msinitcyn/robo-club-3d-models/artifacts/v1.2/lego_base_t.stl

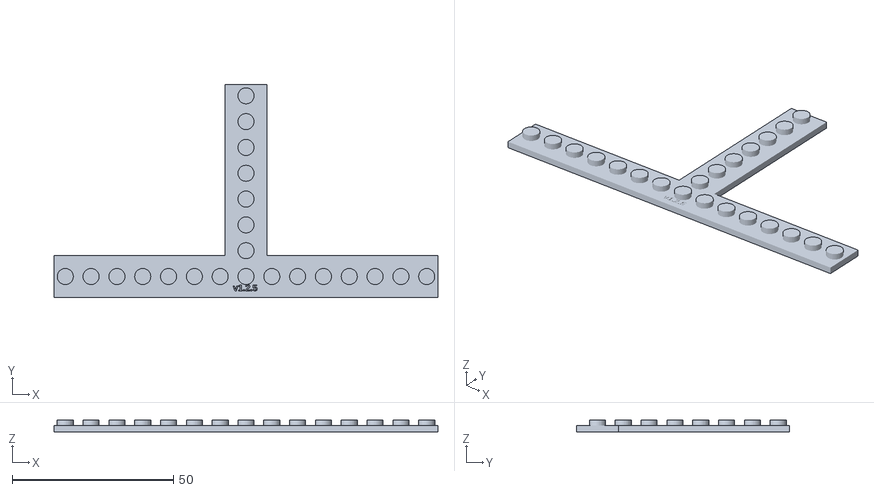
[picture p15: CAD file, 2025-12-20]
artifacts/v1.2/lego_base_t.stl
119.0 x 66.0 x 3.80
