msinitcyn/robo-club-3d-models/artifacts/current/lego_base_t.stl

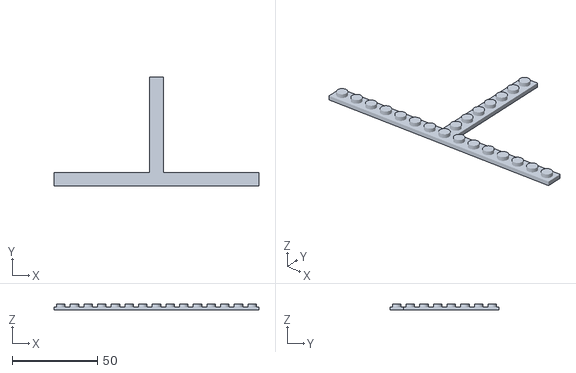
[picture p16: CAD file, 2025-12-21]
artifacts/current/lego_base_t.stl
120.0 x 64.0 x 3.80
