msinitcyn/robo-club-3d-models/artifacts/v1.2/corner_joint_dowel_flexible.stl

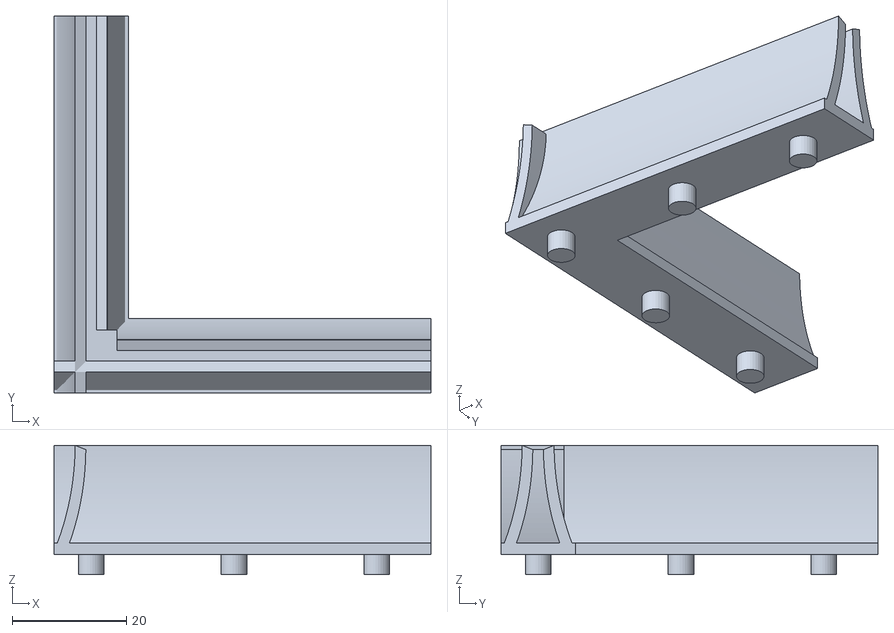
[picture p17: CAD file, 2025-12-20]
artifacts/v1.2/corner_joint_dowel_flexible.stl
66.0 x 66.0 x 22.6
