msinitcyn/robo-club-3d-models/artifacts/v1.2/lego_base_straight.stl

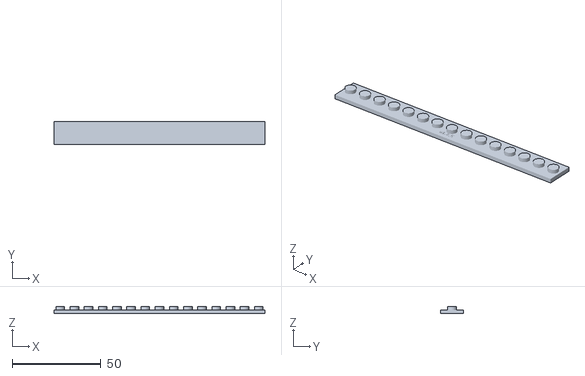
[picture p18: CAD file, 2025-12-20]
artifacts/v1.2/lego_base_straight.stl
119.0 x 13.0 x 3.80
