msinitcyn/robo-club-3d-models/artifacts/current/t_joint_dowel.stl

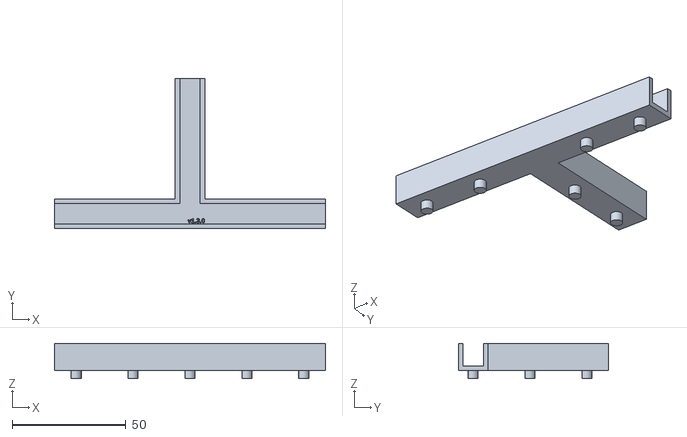
[picture p19: CAD file, 2025-12-21]
artifacts/current/t_joint_dowel.stl
119.0 x 66.0 x 15.5
