msinitcyn/robo-club-3d-models/artifacts/current/cross_joint_dowel.stl

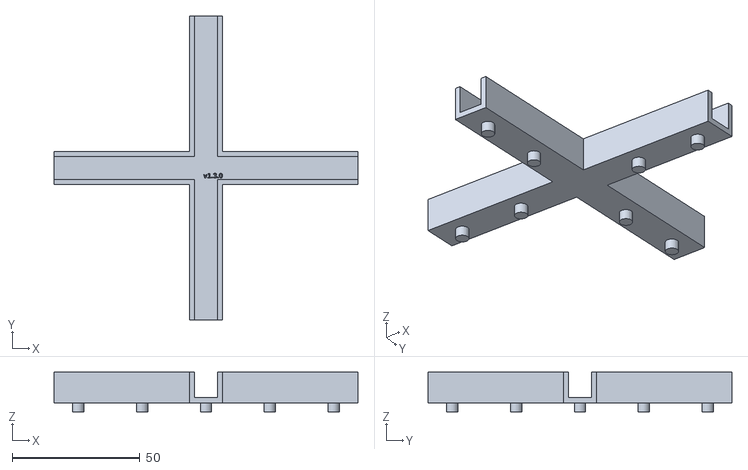
[picture p21: CAD file, 2025-12-21]
artifacts/current/cross_joint_dowel.stl
119.0 x 119.0 x 15.5
