msinitcyn/robo-club-3d-models/artifacts/current/lego_base_cross.stl

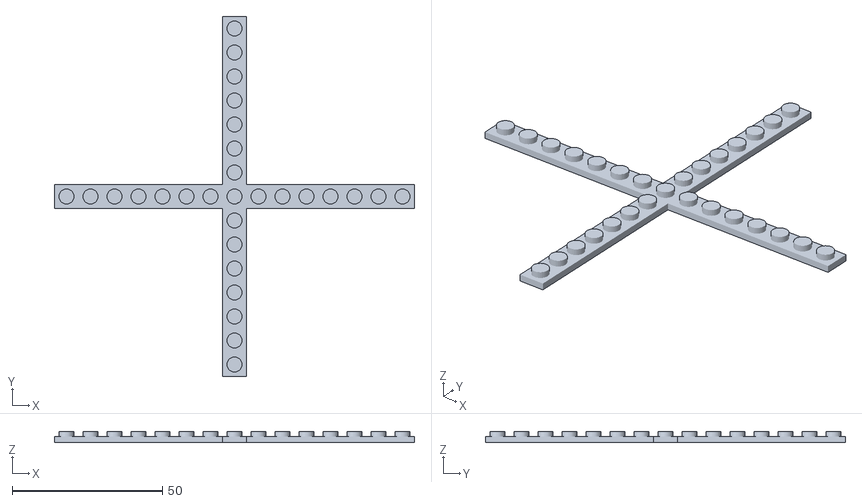
[picture p23: CAD file, 2025-12-21]
artifacts/current/lego_base_cross.stl
120.0 x 120.0 x 3.80
