msinitcyn/robo-club-3d-models/artifacts/current/lego_base_t_dowel.stl

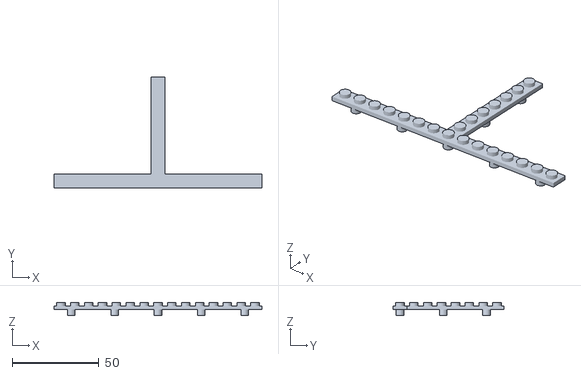
[picture p25: CAD file, 2025-12-21]
artifacts/current/lego_base_t_dowel.stl
120.0 x 64.0 x 7.30
