msinitcyn/robo-club-3d-models/artifacts/current/lego_wall_sleeve_flexible.stl

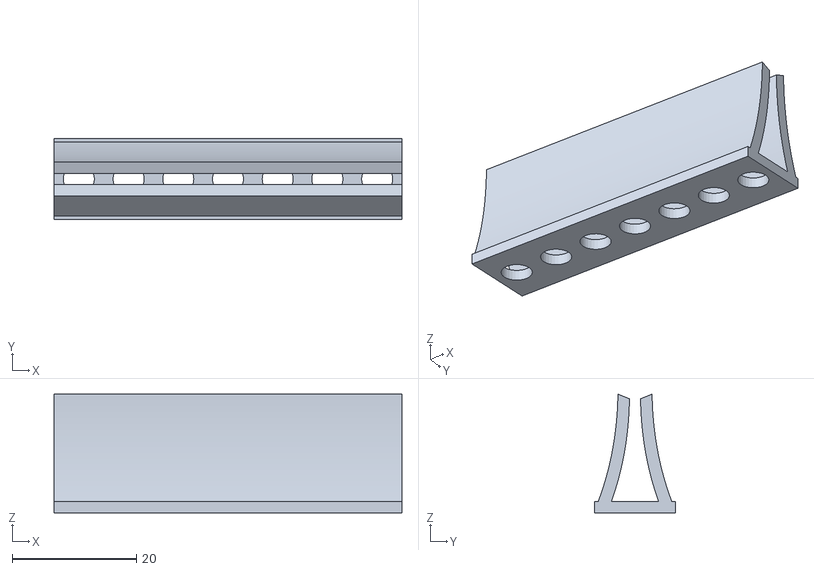
[picture p27: CAD file, 2025-12-21]
artifacts/current/lego_wall_sleeve_flexible.stl
56.0 x 13.0 x 19.1
