msinitcyn/robo-club-3d-models/artifacts/v1.2/straight_joint_dowel.stl

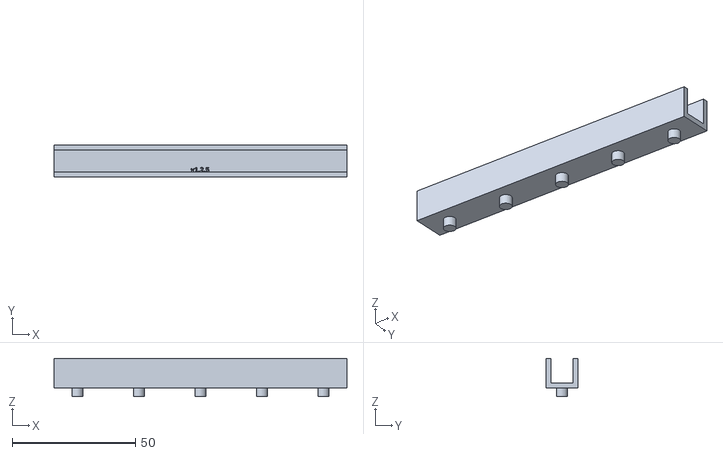
[picture p28: CAD file, 2025-12-20]
artifacts/v1.2/straight_joint_dowel.stl
119.0 x 13.0 x 15.5
