msinitcyn/robo-club-3d-models/artifacts/current/lego_base_cross_dowel.stl

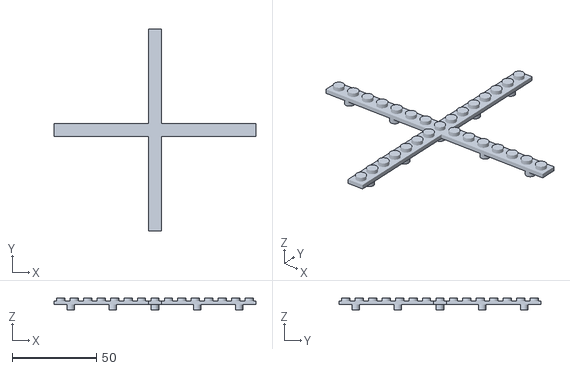
[picture p29: CAD file, 2025-12-21]
artifacts/current/lego_base_cross_dowel.stl
120.0 x 120.0 x 7.30
