msinitcyn/robo-club-3d-models/artifacts/current/lego_base_straight.stl

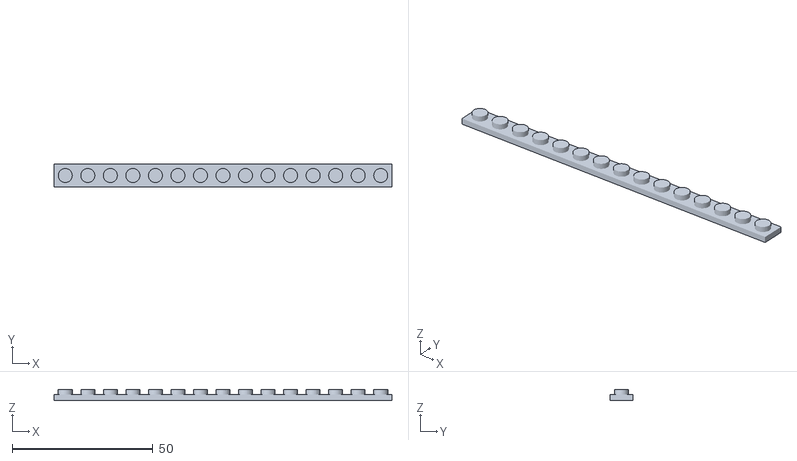
[picture p30: CAD file, 2025-12-21]
artifacts/current/lego_base_straight.stl
120.0 x 8.00 x 3.80
