msinitcyn/robo-club-3d-models/artifacts/current/t_joint_flexible.stl

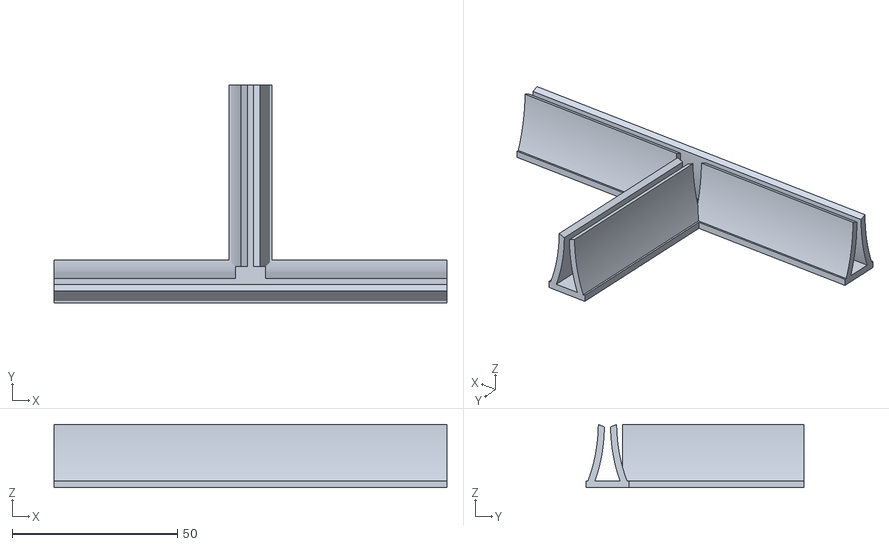
[picture p32: CAD file, 2025-12-21]
artifacts/current/t_joint_flexible.stl
119.0 x 66.0 x 19.1
