msinitcyn/robo-club-3d-models/artifacts/v1.2/lego_base_cross_dowel.stl

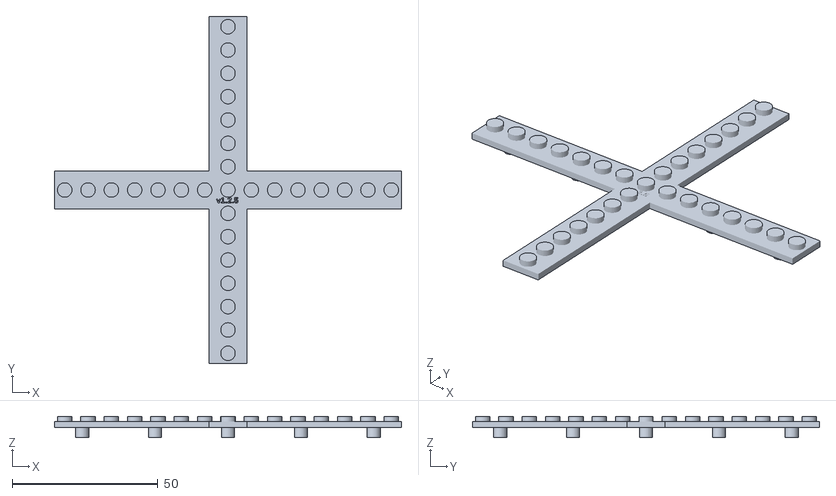
[picture p33: CAD file, 2025-12-20]
artifacts/v1.2/lego_base_cross_dowel.stl
119.0 x 119.0 x 7.30
