msinitcyn/robo-club-3d-models/artifacts/v1.2/lego_wall_sleeve_flexible.stl

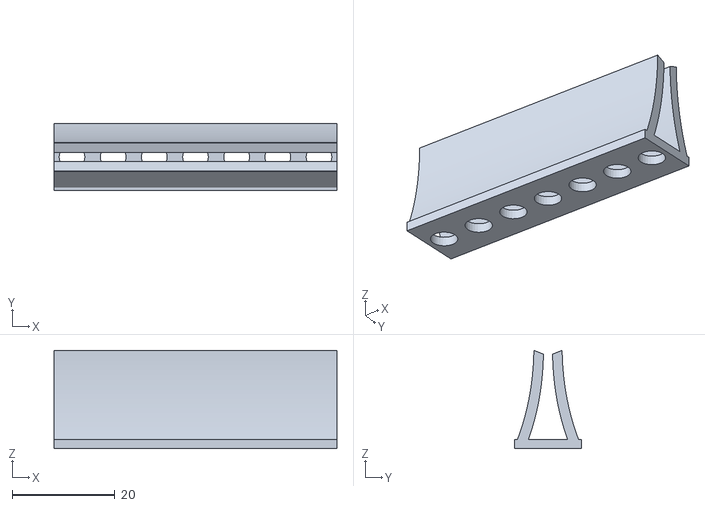
[picture p34: CAD file, 2025-12-20]
artifacts/v1.2/lego_wall_sleeve_flexible.stl
55.0 x 13.0 x 19.1
