msinitcyn/robo-club-3d-models/artifacts/v1.2/lego_base_corner_dowel.stl

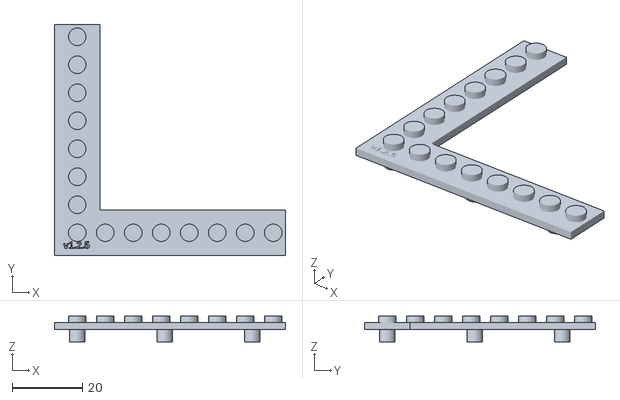
[picture p36: CAD file, 2025-12-20]
artifacts/v1.2/lego_base_corner_dowel.stl
66.0 x 66.0 x 7.30
