msinitcyn/robo-club-3d-models/artifacts/current/cross_joint_flexible.stl

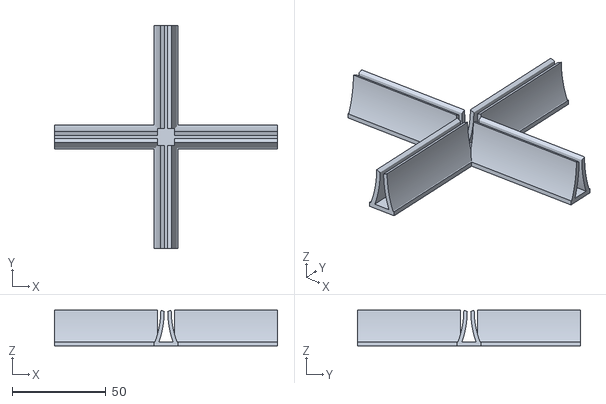
[picture p37: CAD file, 2025-12-21]
artifacts/current/cross_joint_flexible.stl
119.0 x 119.0 x 19.1
