msinitcyn/robo-club-3d-models/artifacts/v1.2/lego_base_t_dowel.stl

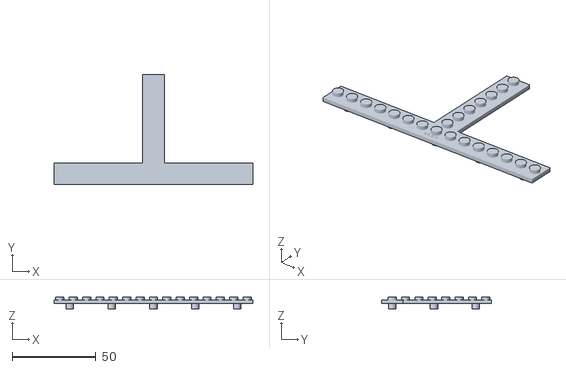
[picture p38: CAD file, 2025-12-20]
artifacts/v1.2/lego_base_t_dowel.stl
119.0 x 66.0 x 7.30
