msinitcyn/robo-club-3d-models/artifacts/v1.2/lego_wall_sleeve.stl

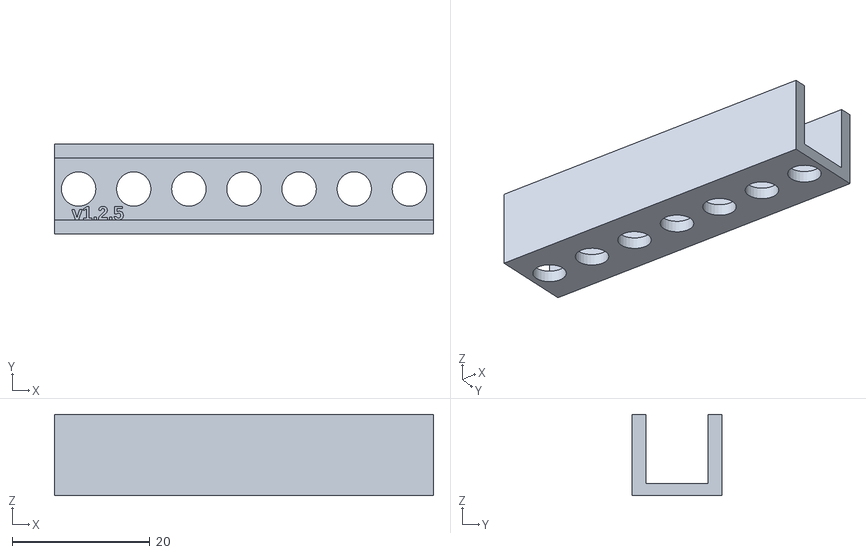
[picture p40: CAD file, 2025-12-19]
artifacts/v1.2/lego_wall_sleeve.stl
55.0 x 13.0 x 11.8
