msinitcyn/robo-club-3d-models/artifacts/current/lego_base_t_double.stl

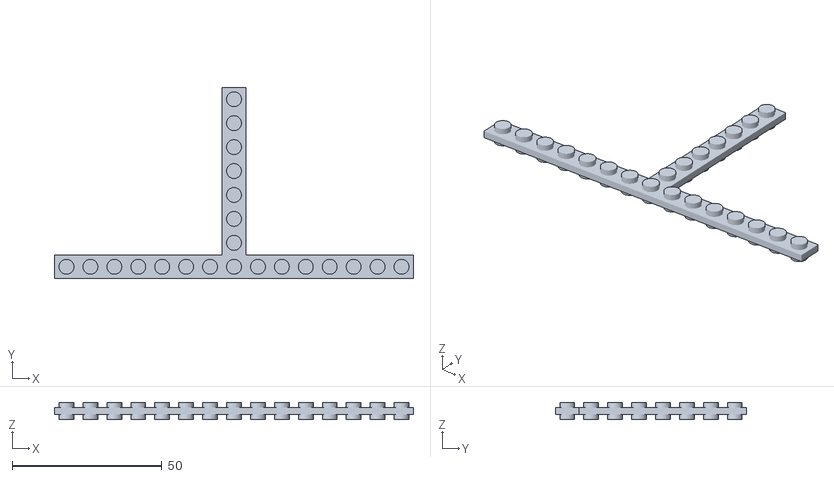
[picture p41: CAD file, 2025-12-21]
artifacts/current/lego_base_t_double.stl
120.0 x 64.0 x 5.80
