msinitcyn/robo-club-3d-models/artifacts/v1.2/cross_joint.stl

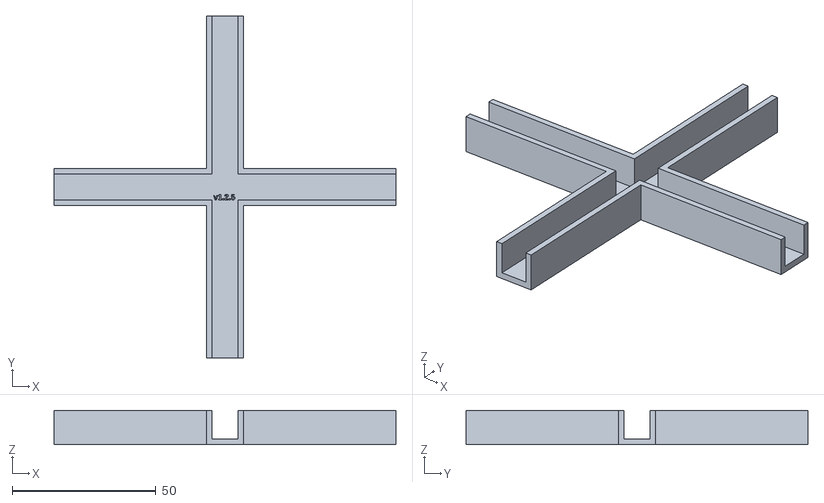
[picture p42: CAD file, 2025-12-19]
artifacts/v1.2/cross_joint.stl
119.0 x 119.0 x 12.0
