msinitcyn/robo-club-3d-models/artifacts/current/end_cap.stl

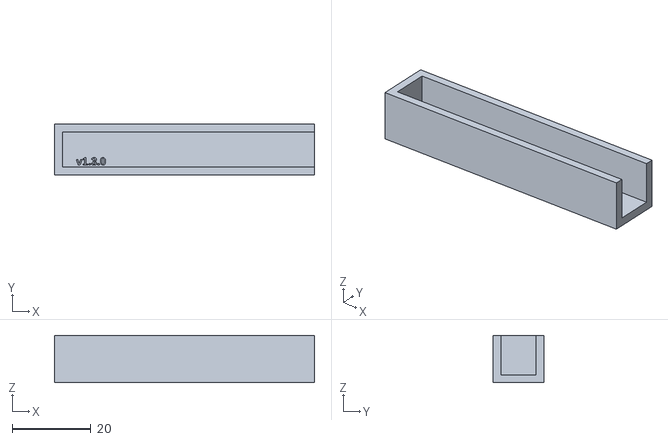
[picture p43: CAD file, 2025-12-21]
artifacts/current/end_cap.stl
66.0 x 13.0 x 12.0
