msinitcyn/robo-club-3d-models/artifacts/v1.2/corner_joint.stl

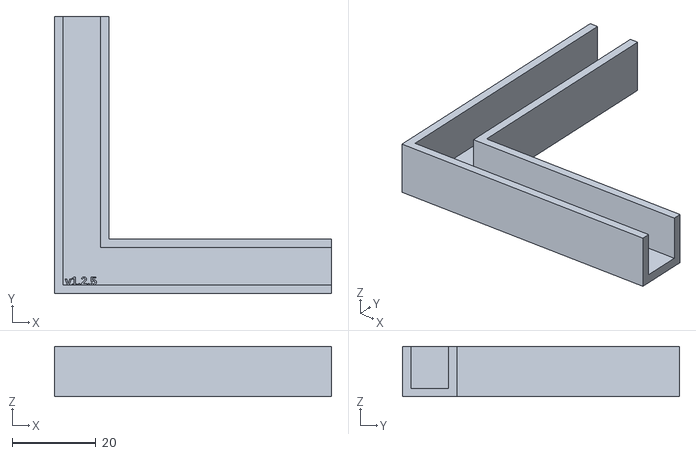
[picture p44: CAD file, 2025-12-19]
artifacts/v1.2/corner_joint.stl
66.0 x 66.0 x 12.0
