msinitcyn/robo-club-3d-models/artifacts/current/lego_wall_sleeve.stl

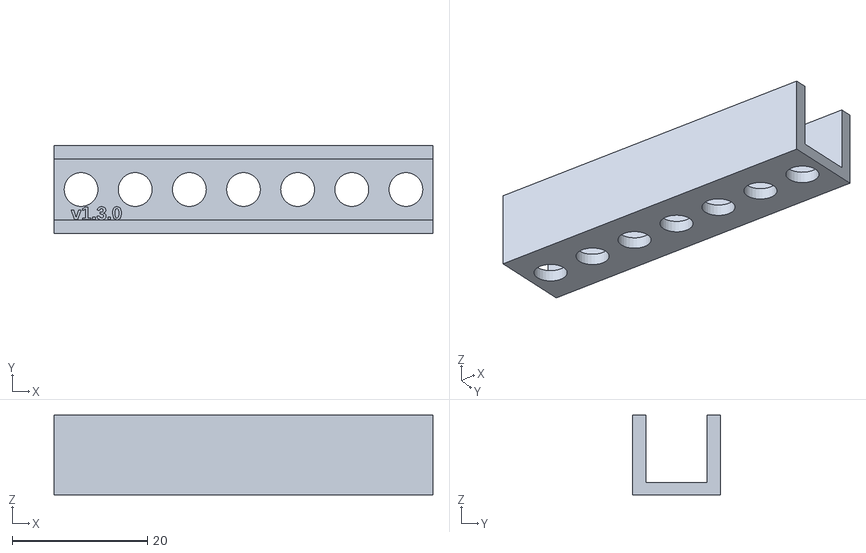
[picture p45: CAD file, 2025-12-21]
artifacts/current/lego_wall_sleeve.stl
56.0 x 13.0 x 11.8
