msinitcyn/robo-club-3d-models/artifacts/v1.2/end_cap_dowel_flexible.stl

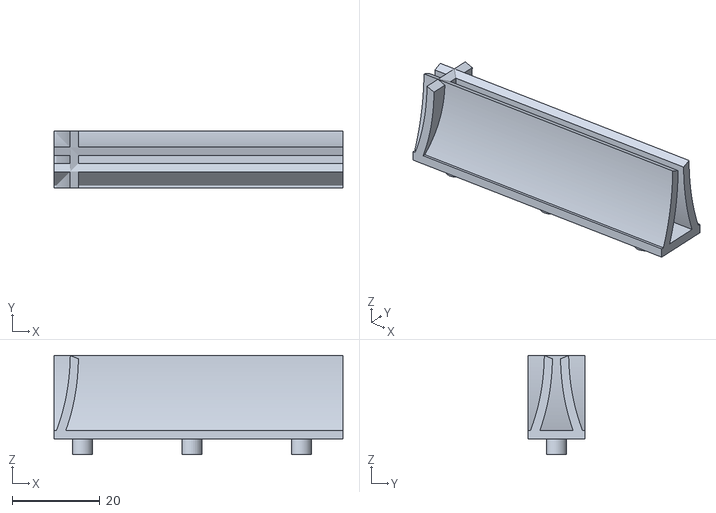
[picture p46: CAD file, 2025-12-19]
artifacts/v1.2/end_cap_dowel_flexible.stl
66.0 x 13.0 x 22.6
