msinitcyn/robo-club-3d-models/artifacts/v1.2/corner_joint_flexible.stl

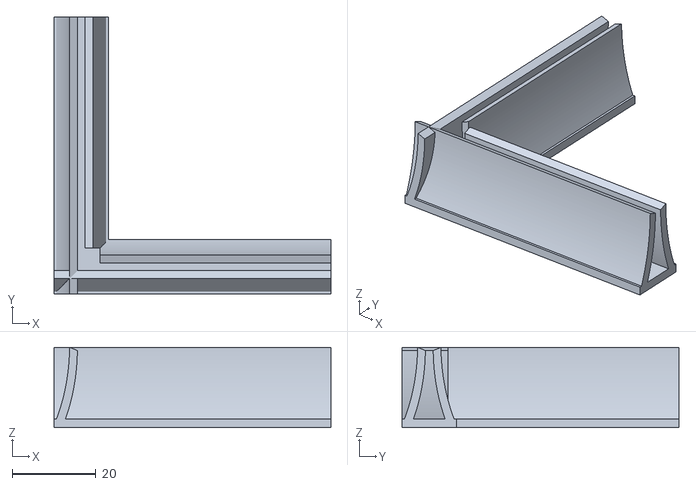
[picture p48: CAD file, 2025-12-19]
artifacts/v1.2/corner_joint_flexible.stl
66.0 x 66.0 x 19.1
