msinitcyn/robo-club-3d-models/artifacts/current/lego_base_corner_dowel.stl

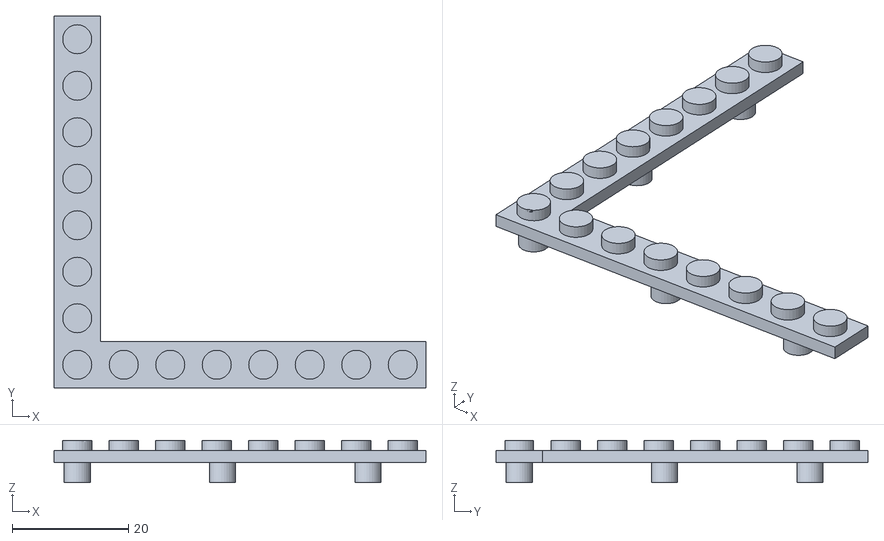
[picture p49: CAD file, 2025-12-21]
artifacts/current/lego_base_corner_dowel.stl
64.0 x 64.0 x 7.30
