msinitcyn/robo-club-3d-models/artifacts/current/end_cap_dowel_flexible.stl

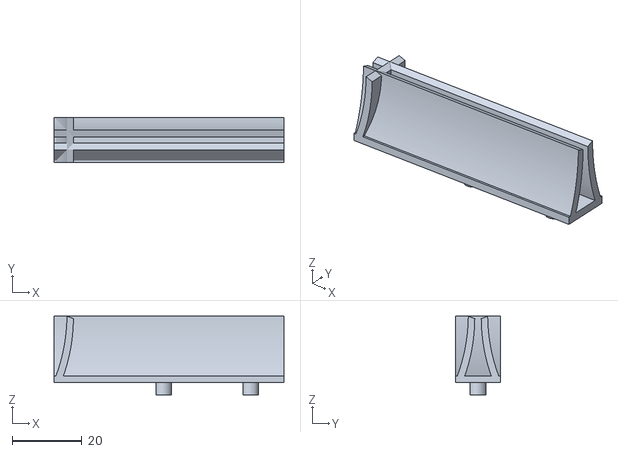
[picture p50: CAD file, 2025-12-21]
artifacts/current/end_cap_dowel_flexible.stl
66.0 x 13.0 x 22.6
