msinitcyn/robo-club-3d-models/artifacts/current/lego_base_cross_double.stl

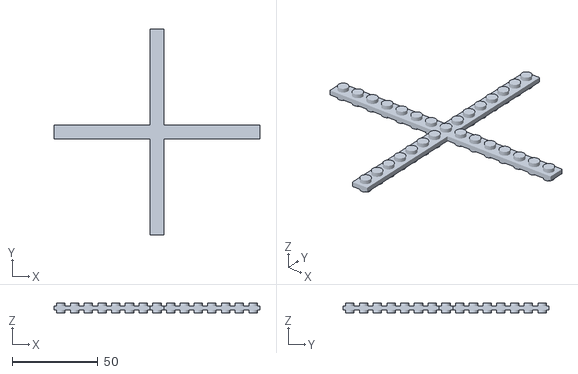
[picture p51: CAD file, 2025-12-21]
artifacts/current/lego_base_cross_double.stl
120.0 x 120.0 x 5.80
