msinitcyn/robo-club-3d-models/artifacts/current/lego_base_straight_dowel.stl

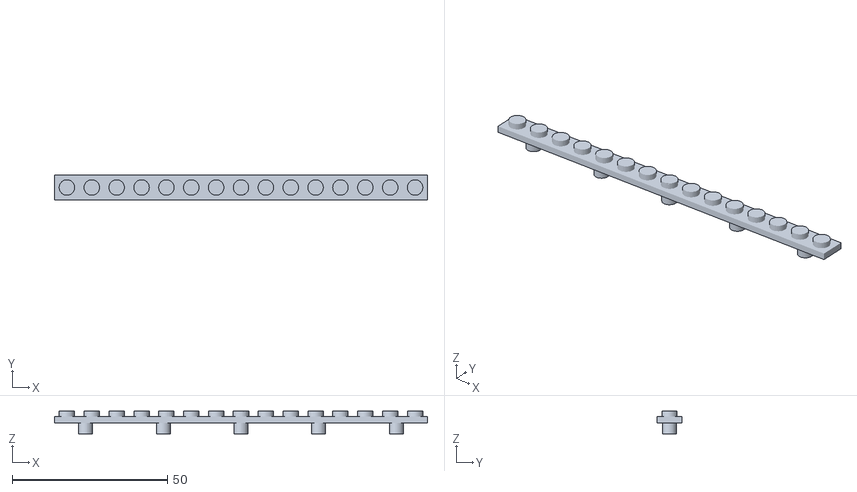
[picture p52: CAD file, 2025-12-21]
artifacts/current/lego_base_straight_dowel.stl
120.0 x 8.00 x 7.30
