msinitcyn/robo-club-3d-models/maze/scad/corner_joint.scad

include <common.scad>
use <version.scad>

difference() {
    union() {
        place_center_base();
        place_center_wall(2);
        place_center_wall(3);

        orient_sleeve(0) {
            union() {
                place_sleeve_base(SLEEVE_LENGTH, TOTAL_WIDTH);
                place_sleeve_walls(SLEEVE_LENGTH);
            }
        }

        orient_sleeve(1) {
            union() {
                place_sleeve_base(SLEEVE_LENGTH, TOTAL_WIDTH);
                place_sleeve_walls(SLEEVE_LENGTH);
            }
        }
    }

    print_version();
}
