msinitcyn/robo-club-3d-models/maze/scad/corner_joint_dowel_flexible.scad

include <common.scad>
use <version.scad>

difference() {
    union() {
        place_center_base(with_dowel = true);
        place_center_wall(2, wall_type = "flexible");
        place_center_wall(3, wall_type = "flexible");

        orient_sleeve(0) {
            union() {
                place_sleeve_base(SLEEVE_LENGTH, TOTAL_WIDTH);
                place_sleeve_walls(SLEEVE_LENGTH, "flexible");
                place_sleeve_dowels(SLEEVE_LENGTH);
            }
        }

        orient_sleeve(1) {
            union() {
                place_sleeve_base(SLEEVE_LENGTH, TOTAL_WIDTH);
                place_sleeve_walls(SLEEVE_LENGTH, "flexible");
                place_sleeve_dowels(SLEEVE_LENGTH);
            }
        }
    }

    print_version();
}
