msinitcyn/robo-club-3d-models/maze/scad/t_joint_flexible.scad

include <common.scad>
use <version.scad>

difference() {
    union() {
        place_center_base();
        place_center_wall(3, wall_type = "flexible");

        orient_sleeve(0) {
            union() {
                place_sleeve_base(SLEEVE_LENGTH, TOTAL_WIDTH);
                place_sleeve_walls(SLEEVE_LENGTH, "flexible");
            }
        }

        orient_sleeve(1) {
            union() {
                place_sleeve_base(SLEEVE_LENGTH, TOTAL_WIDTH);
                place_sleeve_walls(SLEEVE_LENGTH, "flexible");
            }
        }

        orient_sleeve(2) {
            union() {
                place_sleeve_base(SLEEVE_LENGTH, TOTAL_WIDTH);
                place_sleeve_walls(SLEEVE_LENGTH, "flexible");
            }
        }
    }

    print_version();
}
